johannesstrueber/dots/kicad_main/display.kicad_sch

## KiCad design kicad_main/display.kicad_sch (2024-08-29)

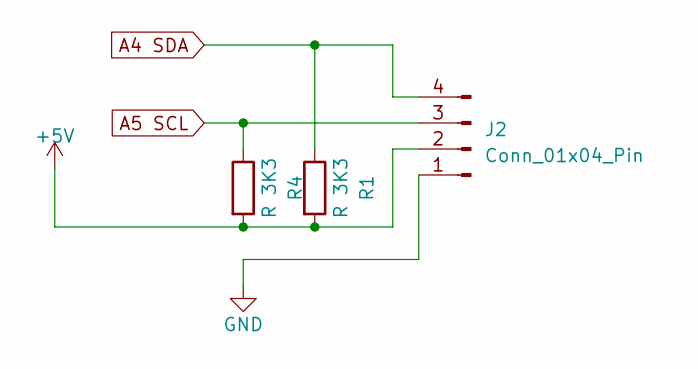
[picture p4: schematic display.kicad_sch]

Parts:
J2: Conn_01x04_Pin; 128x64OLED
R1, R4: R 3K3; R_0805_2012Metric; LCSC C26010

Connections:
+5V: J2.2, R1.2, R4.2
A4 SDA: J2.4, R1.1
A5 SCL: J2.3, R4.1
GND: J2.1
