johannesstrueber/dots/kicad_main/icsp.kicad_sch

## KiCad design kicad_main/icsp.kicad_sch (2024-08-29)

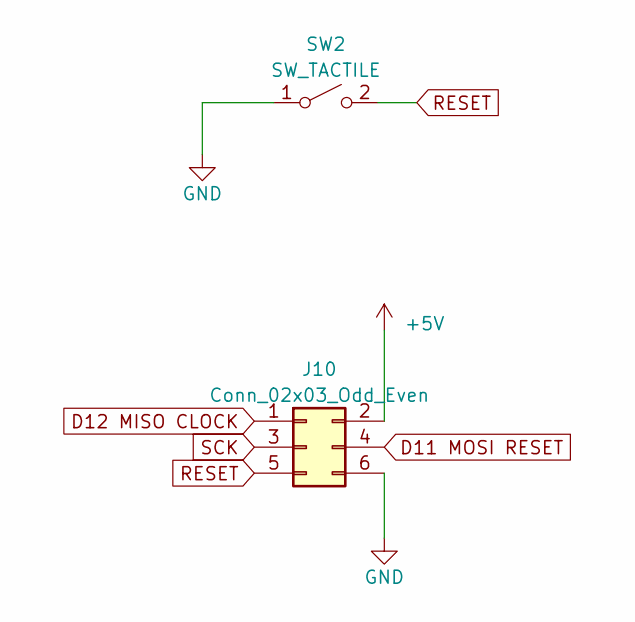
[picture p5: schematic icsp.kicad_sch]

Parts:
J10: Conn_02x03_Odd_Even; PinHeader_2x03_P2.54mm_Vertical; LCSC C492420
SW2: SW_TACTILE; SW_PUSH_6mm

Connections:
+5V: J10.2
D11 MOSI RESET: J10.4
D12 MISO CLOCK: J10.1
GND: J10.6, SW2.1 (A)
RESET: J10.5, SW2.2 (B)
SCK: J10.3
