johannesstrueber/dots/kicad_main/jack_inputs.kicad_sch

## KiCad design kicad_main/jack_inputs.kicad_sch (2024-08-29)

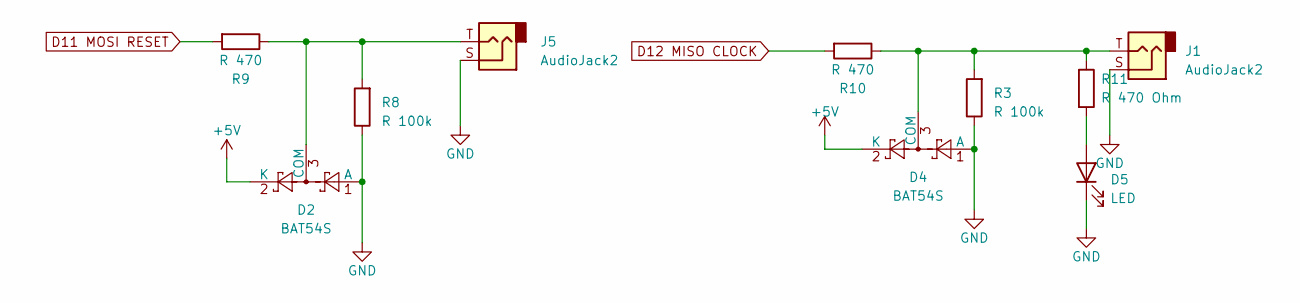
[picture p6: schematic jack_inputs.kicad_sch]

Parts:
D2, D4: BAT54S; SOT-23; LCSC C916425
D5: LED; LED_D3.0mm
J1, J5: AudioJack2; Jack_3.5mm_QingPu_WQP-PJ398SM_Vertical_CircularHoles
R3, R8: R 100k; R_0805_2012Metric; LCSC C149504
R9, R10: R 470; R_0805_2012Metric; LCSC C17710
R11: R 470 Ohm; R_0805_2012Metric; LCSC C17710

Connections:
+5V: D2.2 (K), D4.2 (K)
D11 MOSI RESET: R9.2
D12 MISO CLOCK: R10.2
GND: D2.1 (A), D4.1 (A), D5.1 (K), J1.S, J5.S, R3.1, R8.1
unnamed: D2.3 (COM), J5.T, R8.2, R9.1
unnamed: D4.3 (COM), J1.T, R3.2, R10.1, R11.1
unnamed: D5.2 (A), R11.2
