johannesstrueber/dots/kicad_main/jack_outputs.kicad_sch

## KiCad design kicad_main/jack_outputs.kicad_sch (2024-08-29)

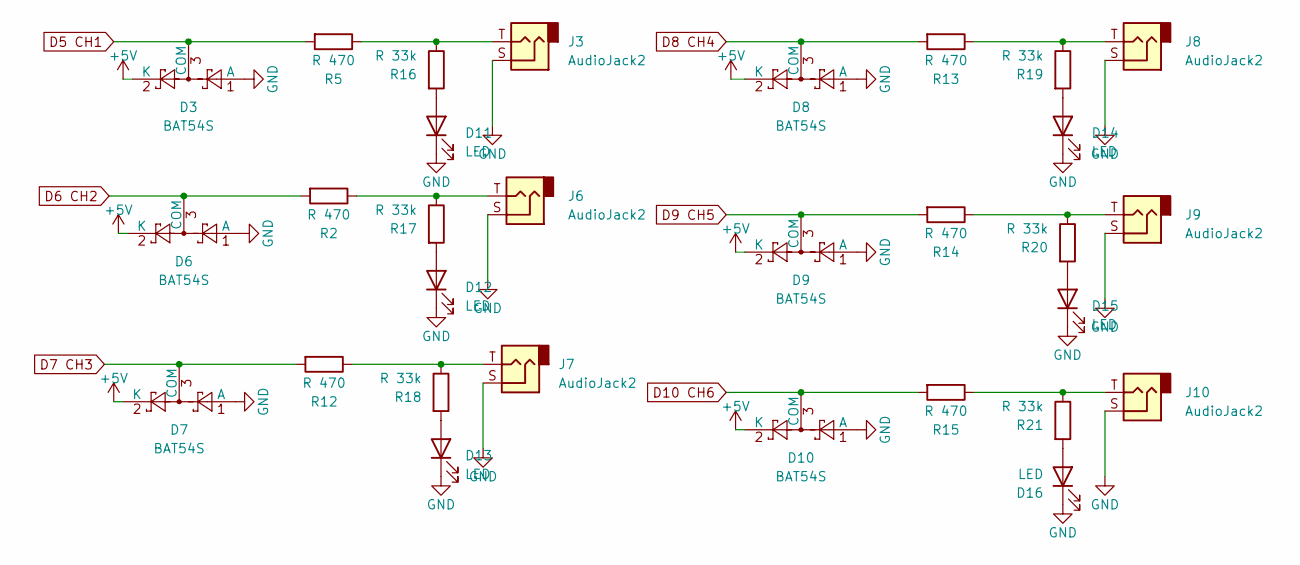
[picture p7: schematic jack_outputs.kicad_sch]

Parts:
D3, D6, D7, D8, D9, D10: BAT54S; SOT-23; LCSC C916425
D11, D12, D13, D14, D15, D16: LED; LED_D2.0mm_W4.0mm_H2.8mm_FlatTop
J3, J6, J7, J8, J9, J10: AudioJack2; Jack_3.5mm_QingPu_WQP-PJ398SM_Vertical_CircularHoles
R2, R5, R12, R13, R14, R15: R 470; R_0805_2012Metric; LCSC C17710
R16, R17, R18, R19, R20, R21: R 33k; R_0805_2012Metric; LCSC C17633

Connections:
+5V: D3.2 (K), D6.2 (K), D7.2 (K), D8.2 (K), D9.2 (K), D10.2 (K)
D5 CH1: D3.3 (COM), R5.2
D6 CH2: D6.3 (COM), R2.2
D7 CH3: D7.3 (COM), R12.2
D8 CH4: D8.3 (COM), R13.2
D9 CH5: D9.3 (COM), R14.2
D10 CH6: D10.3 (COM), R15.2
GND: D3.1 (A), D6.1 (A), D7.1 (A), D8.1 (A), D9.1 (A), D10.1 (A), D11.1 (K), D12.1 (K), D13.1 (K), D14.1 (K), D15.1 (K), D16.1 (K), J3.S, J6.S, J7.S, J8.S, J9.S, J10.S
unnamed: D11.2 (A), R16.2
unnamed: D12.2 (A), R17.2
unnamed: D13.2 (A), R18.2
unnamed: D14.2 (A), R19.2
unnamed: D15.2 (A), R20.2
unnamed: D16.2 (A), R21.2
unnamed: J3.T, R5.1, R16.1
unnamed: J6.T, R2.1, R17.1
unnamed: J7.T, R12.1, R18.1
unnamed: J8.T, R13.1, R19.1
unnamed: J9.T, R14.1, R20.1
unnamed: J10.T, R15.1, R21.1
