johannesstrueber/dots/kicad_main/main.kicad_sch

## KiCad design kicad_main/main.kicad_sch (2024-08-29)

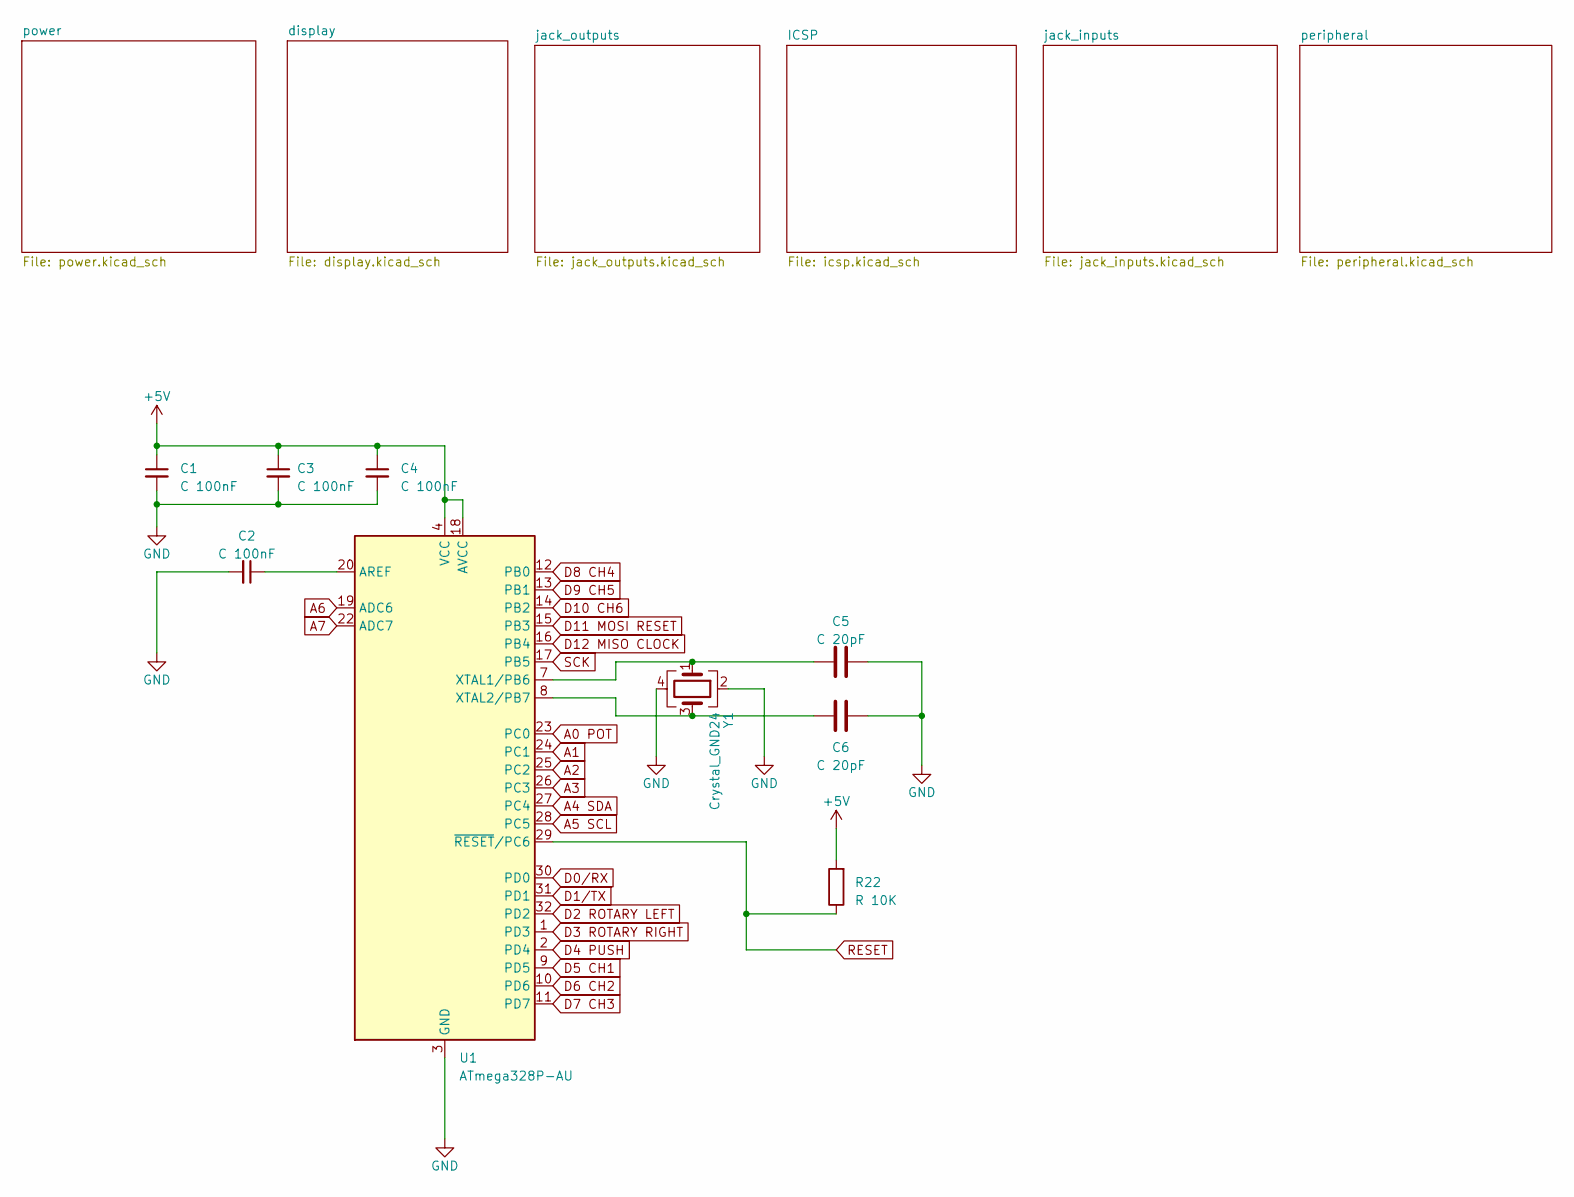
[picture p8: schematic main.kicad_sch]

Parts:
C1, C2, C3, C4: C 100nF; C_0805_2012Metric; LCSC C49678
C5, C6: C 20pF; C_0603_1608Metric; LCSC C1648
R22: R 10K; R_0805_2012Metric; LCSC C17414
U1: ATmega328P-AU; TQFP-32_7x7mm_P0.8mm; LCSC C14877
Y1: Crystal_GND24; Crystal_SMD_3225-4Pin_3.2x2.5mm; LCSC C13738

Connections:
+5V: C1.1, C3.1, C4.1, R22.2, U1.4 (VCC), U1.6 (VCC), U1.18 (AVCC)
A0 POT: U1.23 (PC0)
A1: U1.24 (PC1)
A2: U1.25 (PC2)
A3: U1.26 (PC3)
A4 SDA: U1.27 (PC4)
A5 SCL: U1.28 (PC5)
A6: U1.19 (ADC6)
A7: U1.22 (ADC7)
D0/RX: U1.30 (PD0)
D1/TX: U1.31 (PD1)
D2 ROTARY LEFT: U1.32 (PD2)
D3 ROTARY RIGHT: U1.1 (PD3)
D4 PUSH: U1.2 (PD4)
D5 CH1: U1.9 (PD5)
D6 CH2: U1.10 (PD6)
D7 CH3: U1.11 (PD7)
D8 CH4: U1.12 (PB0)
D9 CH5: U1.13 (PB1)
D10 CH6: U1.14 (PB2)
D11 MOSI RESET: U1.15 (PB3)
D12 MISO CLOCK: U1.16 (PB4)
GND: C1.2, C2.2, C3.2, C4.2, C5.2, C6.2, U1.3 (GND), U1.5 (GND), U1.21 (GND), Y1.2, Y1.4
unnamed: C2.1, U1.20 (AREF)
unnamed: C5.1, U1.7 (XTAL1/PB6), Y1.1
unnamed: C6.1, U1.8 (XTAL2/PB7), Y1.3
RESET: R22.1, U1.29 (~RESET/PC6)
SCK: U1.17 (PB5)
