johannesstrueber/dots/kicad_main/peripheral.kicad_sch

## KiCad design kicad_main/peripheral.kicad_sch (2024-09-15)

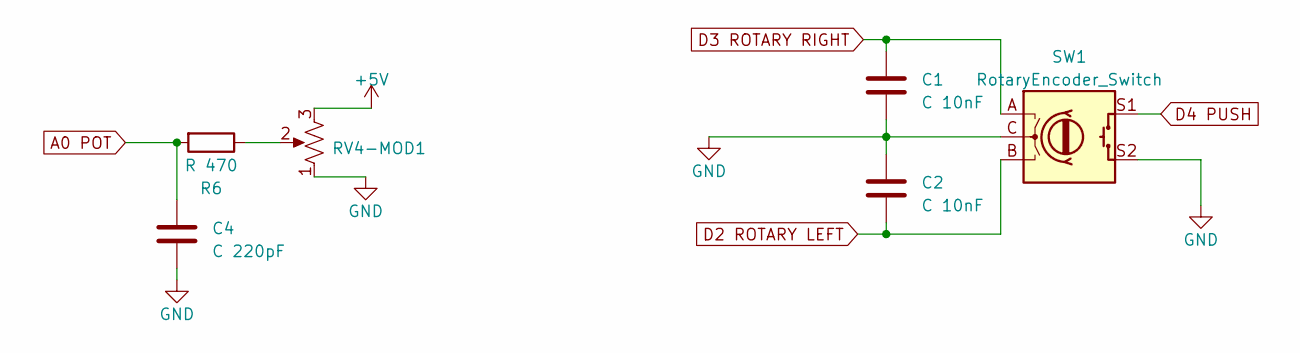
[picture p9: schematic peripheral.kicad_sch]

Parts:
C1, C2: C 10nF; C_0805_2012Metric; LCSC C1710
C4: C 220pF; C_0805_2012Metric; LCSC C107145
R6: R 470; R_0805_2012Metric; LCSC C17710
RV4-MOD1: R_Potentiometer_US_100K; PinSocket_1x03_P2.54mm_Vertical
SW1: RotaryEncoder_Switch; RotaryEncoder_Alps_EC11E-Switch_Vertical_H20mm

Connections:
+5V: RV4-MOD1.3
A0 POT: C4.1, R6.2
D2 ROTARY LEFT: C2.2, SW1.B
D3 ROTARY RIGHT: C1.1, SW1.A
D4 PUSH: SW1.S1
GND: C1.2, C2.1, C4.2, RV4-MOD1.1, SW1.C, SW1.S2
unnamed: R6.1, RV4-MOD1.2
