johannesstrueber/dots/kicad_main/power.kicad_sch

## KiCad design kicad_main/power.kicad_sch (2024-08-29)

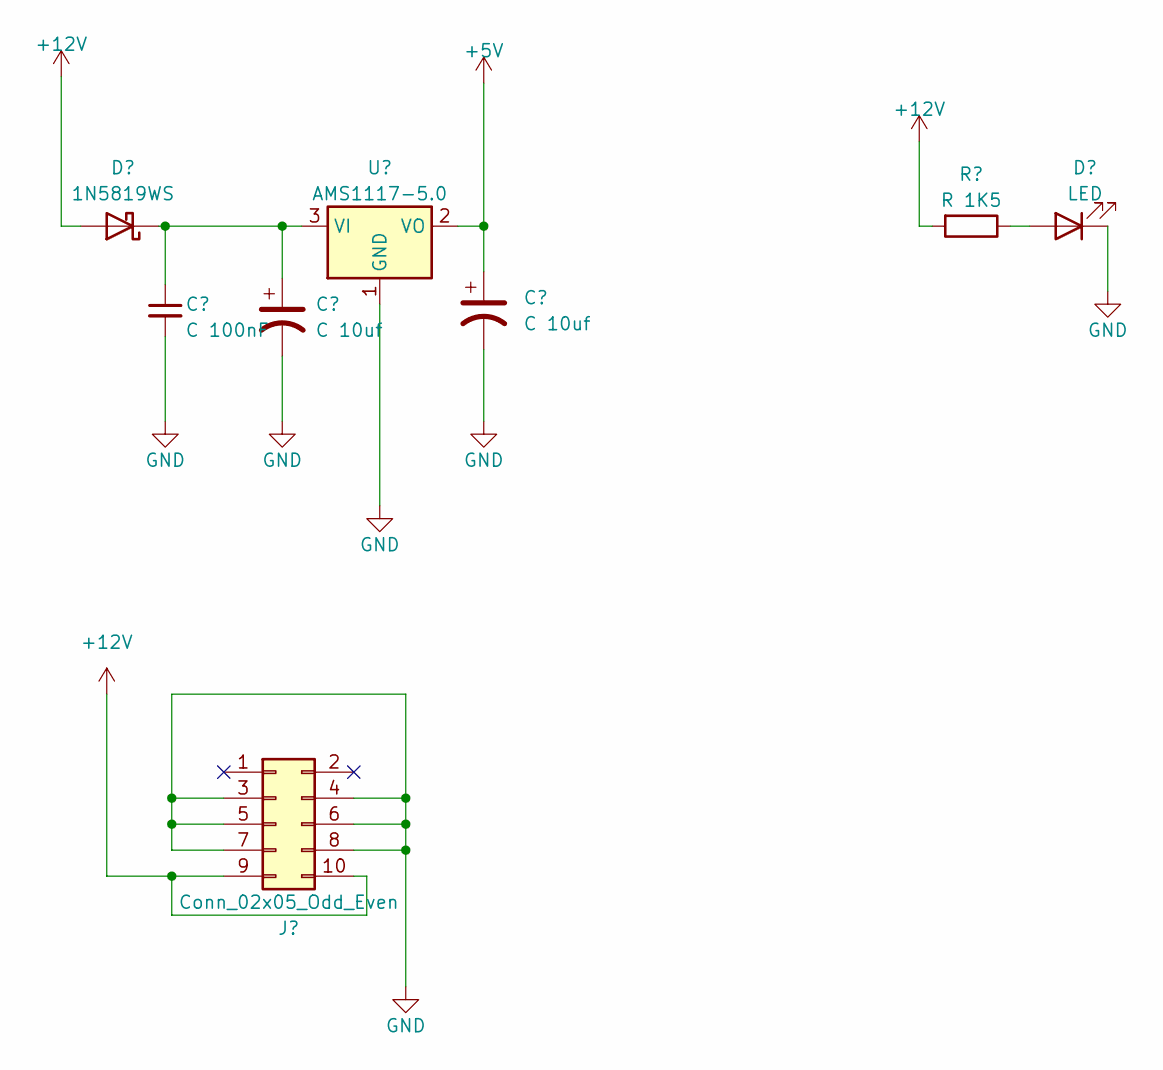
[picture p10: schematic power.kicad_sch]

Parts:
C7: C 100nF; C_0805_2012Metric; LCSC C49678
C8, C9: C 10uf; CP_Elec_5x5.4; LCSC C72486
D1: 1N5819WS; D_SOD-323; LCSC C191023
D2: LED; LED_0805_2012Metric; LCSC C84256
J1: Conn_02x05_Odd_Even; PinHeader_2x05_P2.54mm_Vertical; LCSC C492422
R1: R 1K5; R_0805_2012Metric; LCSC C4310
U2: AMS1117-5.0; SOT-223-3_TabPin2; LCSC C917153

Connections:
+5V: C9.1, U2.2 (VO)
+12V: D1.2 (A), J1.9, J1.10, R1.2
GND: C7.2, C8.2, C9.2, D2.1 (K), J1.3, J1.4, J1.5, J1.6, J1.7, J1.8, U2.1 (GND)
unnamed: C7.1, C8.1, D1.1 (K), U2.3 (VI)
unnamed: D2.2 (A), R1.1
