johannesstrueber/dots/code/include/ClockDivider.h

#ifndef CLOCK_DIVIDER_H
#define CLOCK_DIVIDER_H

#include "utilities/Display.h"
#include "utilities/Encoder.h"
#include "utilities/MenuLayout.h"
#include "utilities/PatternMath.h"
#include "utilities/Trigger.h"
#include <Adafruit_GFX.h>
#include <Adafruit_SSD1306.h>
#include <Arduino.h>
#include <EEPROM.h>
#include <Wire.h>

extern int8_t numChannels;
extern const uint8_t outputPins[];

extern uint8_t bpm;

extern uint8_t stepCount;
extern bool resetIn;
extern bool oldResetIn;
extern bool isPause;
extern bool button;
extern bool oldButton;
extern bool buttonOn;

extern int8_t enc;
extern Adafruit_SSD1306 display;

enum DivEncoderOptions { DIV_ENC_CH1, DIV_ENC_CH2, DIV_ENC_CH3, DIV_ENC_CH4, DIV_ENC_CH5, DIV_ENC_CH6, DIV_ENC_PLAY, DIV_ENC_RESET, DIV_ENC_BACK };

extern uint8_t intClock;
extern bool clkMode;
extern bool outMode;
extern uint8_t page;

extern uint8_t resetMode;
extern int8_t newPosition;
extern int8_t oldPosition;
extern int8_t msDelay;

char divBuffer[5];

extern const char playText[];
extern const char pauseText[];
extern const char backText[];
extern const char unselectedText[];
extern const char channelIndexText[];

extern const char *const resetOptions[];

extern bool updateTrigger;
extern bool updateScreen;

uint8_t channelDividers[6] = {1, 2, 4, 3, 6, 8};

void saveChannelDividers() {
    for (int i = 0; i < 6; i++) {
        EEPROM.write(422 + i, channelDividers[i]);
    }
}

void loadChannelDividers() {
    for (int i = 0; i < 6; i++) {
        uint8_t value = EEPROM.read(422 + i);
        if (value >= 1 && value <= 16) {
            channelDividers[i] = value;
        } else {
            channelDividers[i] = (i == 0) ? 1 : (1 << (i % 4 + 1));
        }
    }
}

void oledClockDivider() {
    DisplayUtils::initDisplay();

    DisplayUtils::drawMenuSeparator();

    DisplayUtils::drawNumberText(0, MenuLayout::MENU_Y_TOP, enc >= DIV_ENC_CH1 && enc <= DIV_ENC_CH6 ? (enc - DIV_ENC_CH1 + 1) : 0, channelIndexText, enc >= DIV_ENC_CH1 && enc <= DIV_ENC_CH6,
                                 divBuffer);
    DisplayUtils::drawStepCounter(32, MenuLayout::MENU_Y_TOP, stepCount, divBuffer);

    DisplayUtils::drawMenuItemProgMem(64, MenuLayout::MENU_Y_TOP, unselectedText, false, divBuffer);
    DisplayUtils::drawMenuItemProgMem(96, MenuLayout::MENU_Y_TOP, isPause ? pauseText : playText, enc == DIV_ENC_PLAY, divBuffer);

    DisplayUtils::drawDelay(0, MenuLayout::MENU_Y_BOTTOM, msDelay, divBuffer);
    DisplayUtils::drawBPM(32, MenuLayout::MENU_Y_BOTTOM, bpm, intClock, clkMode, divBuffer);
    DisplayUtils::drawMenuItemFromArray(64, MenuLayout::MENU_Y_BOTTOM, resetOptions, resetMode, enc == DIV_ENC_RESET, divBuffer);
    DisplayUtils::drawMenuItemProgMem(96, MenuLayout::MENU_Y_BOTTOM, backText, enc == DIV_ENC_BACK, divBuffer);

    for (int i = 0; i < numChannels; i++) {
        int x = (i >= 3) ? (i - 3) * 22 + 40 : i * 22 + 40;
        int y = (i >= 3) ? 32 : 10;

        bool shouldFill = (stepCount % channelDividers[i] == 0);
        bool isChannelSelected = (enc == DIV_ENC_CH1 + i);

        if (shouldFill) {
            display.fillCircle(x, y, 9, WHITE);
            display.setTextColor(BLACK, WHITE);
        } else {
            display.drawCircle(x, y, 9, WHITE);
            display.setTextColor(WHITE, BLACK);
        }

        if (isChannelSelected) {
            display.drawCircle(x, y, 11, WHITE);
        }

        if (channelDividers[i] > 9) {
            display.setCursor(x - 6, y - 3);
        } else {
            display.setCursor(x - 2, y - 3);
        }
        display.print(channelDividers[i]);
    }
    display.display();
}

void clockDividerLoop() {
    bool needsDisplayUpdate = false;
    int8_t oldEnc = enc;

    if (msDelay < 0)
        TriggerUtils::applyDelay(msDelay);

    oldResetIn = resetIn;
    oldButton = button;

    if (outMode)
        TriggerUtils::setAllOutputsLow();

    EncoderUtils::handleEncoderBounds(enc, 0, DIV_ENC_BACK);

    if (enc != oldEnc) {
        needsDisplayUpdate = true;
    }

    if (buttonOn) {
        switch (enc) {
            case DIV_ENC_PLAY:
                EncoderUtils::toggleParameter(isPause);
                needsDisplayUpdate = true;
                break;
            case DIV_ENC_CH1:
            case DIV_ENC_CH2:
            case DIV_ENC_CH3:
            case DIV_ENC_CH4:
            case DIV_ENC_CH5:
            case DIV_ENC_CH6: {
                int channelIndex = enc - DIV_ENC_CH1;
                channelDividers[channelIndex]++;
                if (channelDividers[channelIndex] > 16) {
                    channelDividers[channelIndex] = 1;
                }
                saveChannelDividers();
                needsDisplayUpdate = true;
            } break;
            case DIV_ENC_RESET:
                if (resetMode == 1)
                    resetMode = 0;
                else
                    resetMode++;
                needsDisplayUpdate = true;
                break;
            case DIV_ENC_BACK:
                page = 0;
                updateScreen = true;
                return;
        }
    }

    if (resetIn && !oldResetIn) {
        stepCount = 0;
        oldResetIn = resetIn;
    }

    if (stepCount == 64)
        stepCount = 0;

    if (updateTrigger) {
        for (int i = 0; i < numChannels; i++) {
            bool shouldTrigger = (stepCount % channelDividers[i] == 0);
            TriggerUtils::setOutput(i, shouldTrigger);
        }
        updateTrigger = false;
        needsDisplayUpdate = true;
    }

    if (needsDisplayUpdate || updateScreen) {
        oledClockDivider();
        updateScreen = false;
    }

    TriggerUtils::applyDelay(msDelay);
}

#endif
